Wolfman-F16/uhf-radio/include/uhfVersion.h

/*
 * uhfVersion.h
 *
 *  Created on: 26.06.2011
 *      Author: Wolfgang Engelhard
 *
 * Copyright: (c) 2011 by Wolfgang Engelhard
 * License: GNU GPL v2 (see License.txt)
 */

#ifndef UHFVERSION_H_
#define UHFVERSION_H_

const uint8_t chVersion[] = "R-";
const uint8_t freqVersion[] = "000028";

#endif /* UHFVERSION_H_ */
