Wolfman-F16/uhf-radio/include/usbKeyDefs.h

/*
 * usbKeyDefs.h
 *
 *  Created on: 07.09.2011
 *      Author: Wolfgang Engelhard
 *
 * Copyright: (c) 2011 by Wolfgang Engelhard
 * License: GNU GPL v2 (see License.txt)
 */

#ifndef USBKEYDEFS_H_
#define USBKEYDEFS_H_

typedef enum {
  NOT_USED,
  KEY_OFF,
  KEY_MAIN,
  KEY_BOTH,
  KEY_ADF,
  KEY_MNL,
  KEY_PRESET,
  KEY_GUARD,
  KEY_CH_INC,
  KEY_CH_DEC,
  KEY_1_2,
  KEY_1_3,
  KEY_1_4,
  KEY_2_0,
  KEY_2_1,
  KEY_2_2,
  KEY_2_3,
  KEY_2_4,
  KEY_2_5,
  KEY_2_6,
  KEY_2_7,
  KEY_2_8,
  KEY_2_9,
  KEY_3_0,
  KEY_3_1,
  KEY_3_2,
  KEY_3_3,
  KEY_3_4,
  KEY_3_5,
  KEY_3_6,
  KEY_3_7,
  KEY_3_8,
  KEY_3_9,
  KEY_4_0,
  KEY_4_1,
  KEY_4_2,
  KEY_4_3,
  KEY_4_4,
  KEY_4_5,
  KEY_4_6,
  KEY_4_7,
  KEY_4_8,
  KEY_4_9,
  KEY_5_00,
  KEY_5_25,
  KEY_5_50,
  KEY_5_75
} keyCode_e;

#endif /* USBKEYDEFS_H_ */
